satsha-utilities/satsha-ttl/media/cut.png

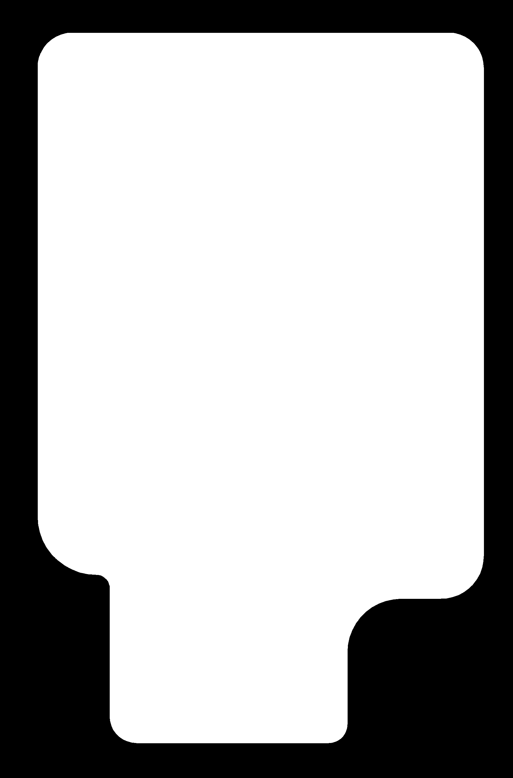
media/cut.png
